MG-5/nixie-clock-hardware/LTSpice/LT3757_Boost-177V.asc

C1: cap; 2.2µ
C2: cap; 6.8n
C3: polcap; 10µ
C4: cap; 47n
C5: cap; 100p
C6: cap; 10n
C7: cap; 420n
C8: cap; 10µ
D1: diode; ES1D
I1: load2; PULSE(0 10m 5m 15µ 15µ 500µ 550u)
L1: ind; 470µ; Rser=170m
Q1: NMOS; FDS2734
R1: RES; 24.3k
R2: res; 5.1k
R3: res; 560k
R4: res; 47k
R5: res; 43.2K
R6: res; 200K
R7: res; 220m
R8: res; 22
Rload: res; 1000000k
U1: LT3757
V1: VOLTAGE; 24; Rser=1
Named nets: 0, OUT, IN
.tran 15m startup
LT3757 - Boost Topology
Input: 24V       Output: 177V@35mA
